dcooperdalrymple/pico_synth_sandbox-hardware/3dmodels/raspberry-pi-pico/RT6150B-33GQW.step

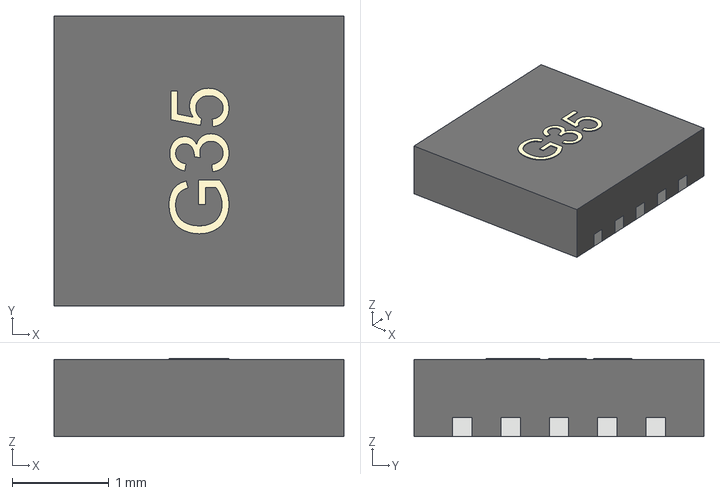
[picture p20: CAD file, 2023-11-14]
3dmodels/raspberry-pi-pico/RT6150B-33GQW.step
3.00 x 3.00 x 0.81 mm
