dcooperdalrymple/pico_synth_sandbox-hardware/3dmodels/SJ1-3525N/ST-212.step

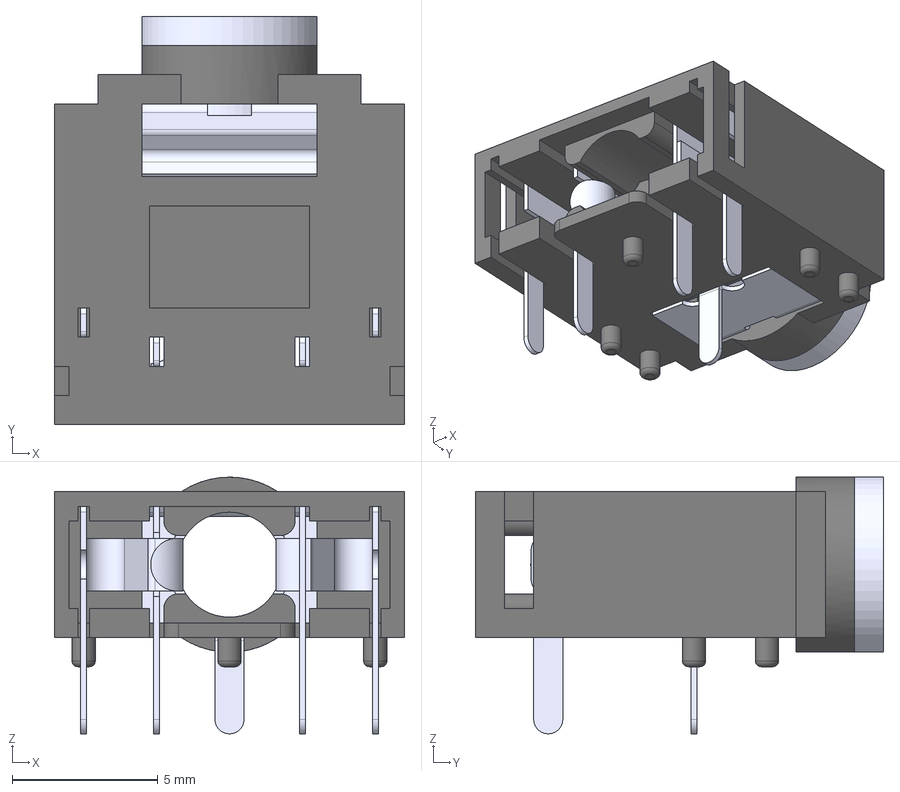
[picture p21: CAD file, 2023-11-14]
3dmodels/SJ1-3525N/ST-212.step
12.0 x 14.0 x 8.80 mm
