dcooperdalrymple/pico_synth_sandbox-hardware/case/rev2/pico_synth_sandbox-Rev2-Bottom.stl

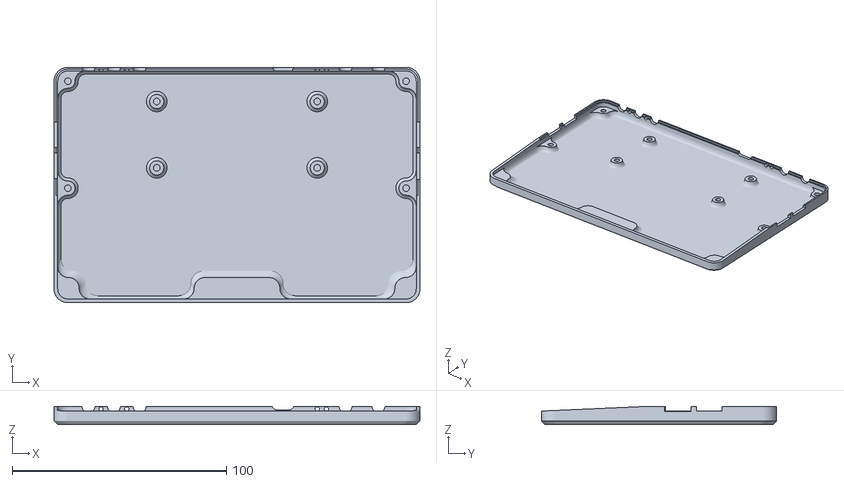
[picture p22: CAD file, 2024-02-06]
case/rev2/pico_synth_sandbox-Rev2-Bottom.stl
171.0 x 110.0 x 8.55
