dcooperdalrymple/pico_synth_sandbox-hardware/3dmodels/PJ320D/PJ320D-Pin-B.SLDPRT

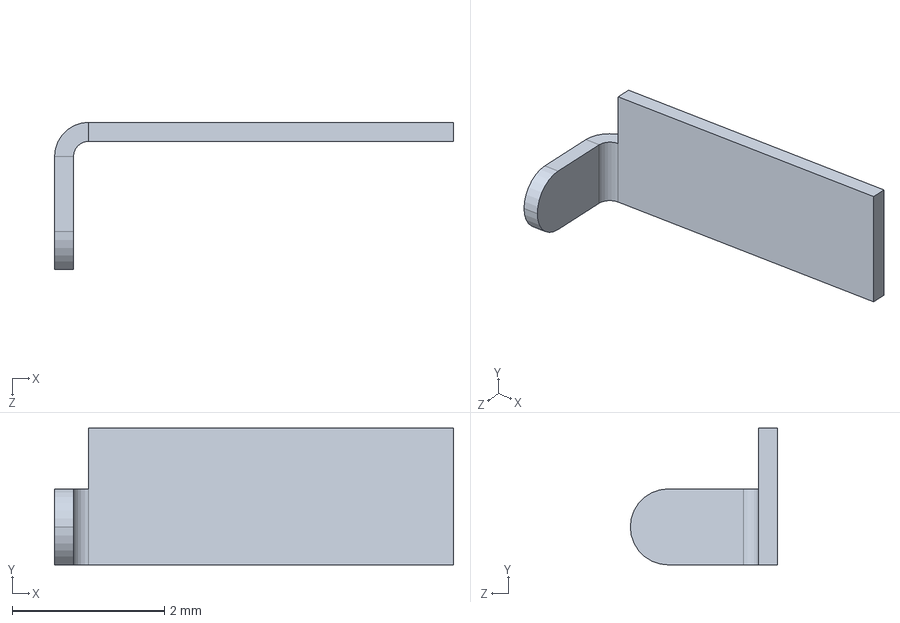
[picture p23: CAD file, 2024-01-01]
3dmodels/PJ320D/PJ320D-Pin-B.SLDPRT
5.25 x 1.80 x 1.94 mm
