dcooperdalrymple/pico_synth_sandbox-hardware/3dmodels/raspberry-pi-pico/C0603.step

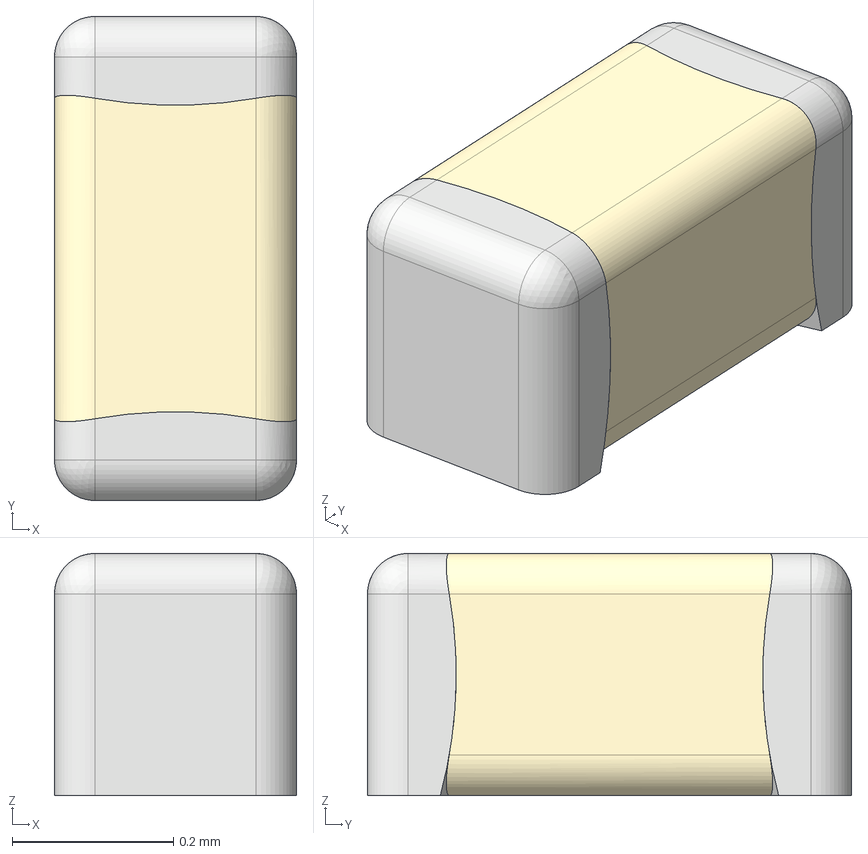
[picture p24: CAD file, 2023-11-14]
3dmodels/raspberry-pi-pico/C0603.step
0.3 x 0.6 x 0.3 mm
