dcooperdalrymple/pico_synth_sandbox-hardware/case/rev2/pico_synth_sandbox-Rev2-Switch.stl

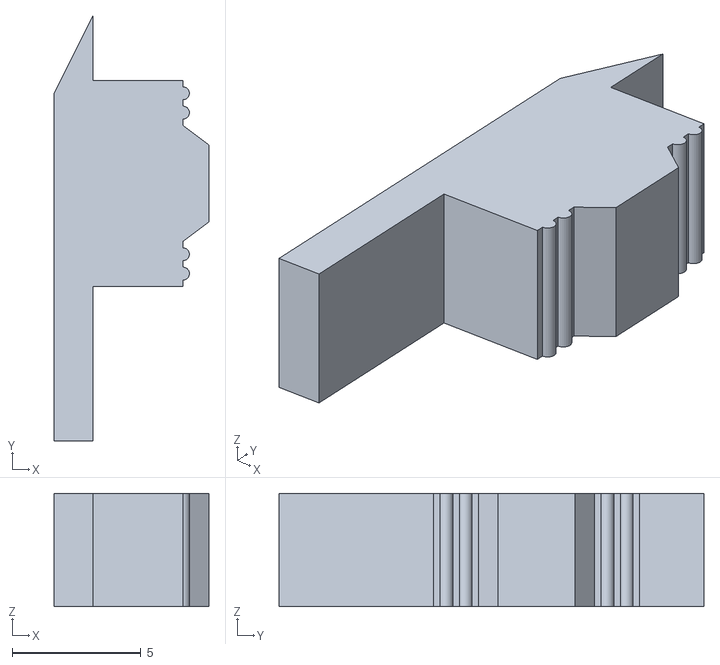
[picture p25: CAD file, 2024-02-06]
case/rev2/pico_synth_sandbox-Rev2-Switch.stl
6.00 x 16.5 x 4.40
