dcooperdalrymple/pico_synth_sandbox-hardware/3dmodels/PJ320D/PJ320A.SLDPRT

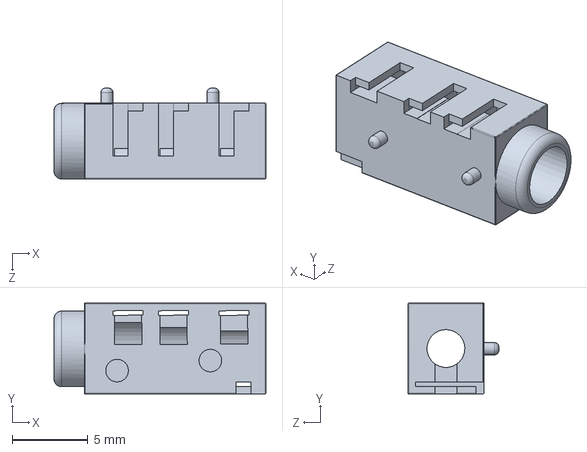
[picture p26: CAD file, 2024-01-01]
3dmodels/PJ320D/PJ320A.SLDPRT
14.0 x 6.00 x 6.00 mm
