dcooperdalrymple/pico_synth_sandbox-hardware/3dmodels/raspberry-pi-pico/R0603.step

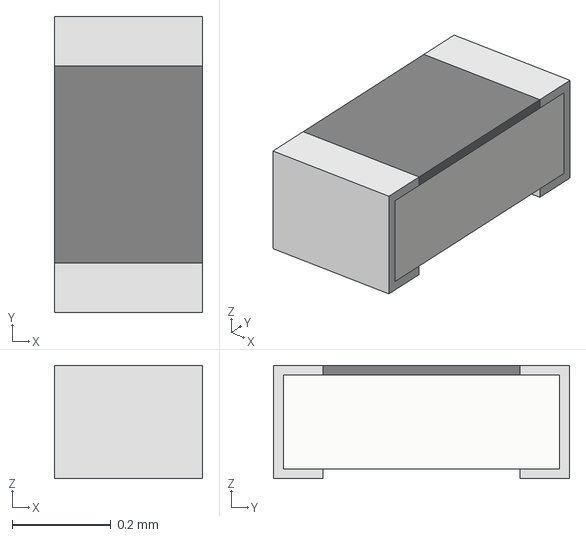
[picture p27: CAD file, 2023-11-14]
3dmodels/raspberry-pi-pico/R0603.step
0.3 x 0.6 x 0.23 mm
