dcooperdalrymple/pico_synth_sandbox-hardware/case/rev2/pico_synth_sandbox-Rev2-LcdHeader.stl

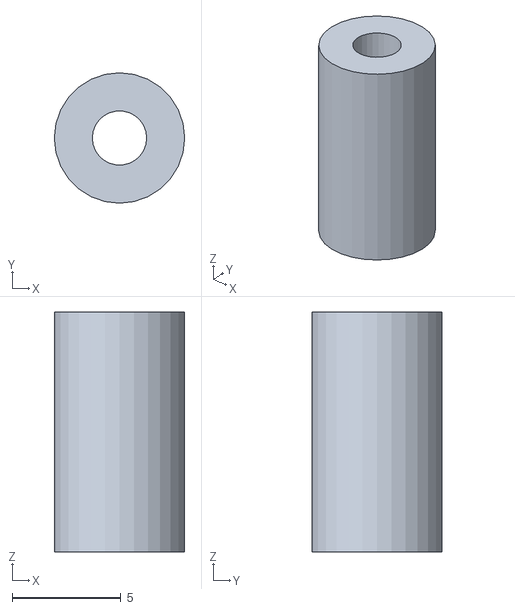
[picture p28: CAD file, 2024-02-06]
case/rev2/pico_synth_sandbox-Rev2-LcdHeader.stl
6.00 x 6.00 x 11.0
