dcooperdalrymple/pico_synth_sandbox-hardware/3dmodels/raspberry-pi-pico/TactSwitch.step

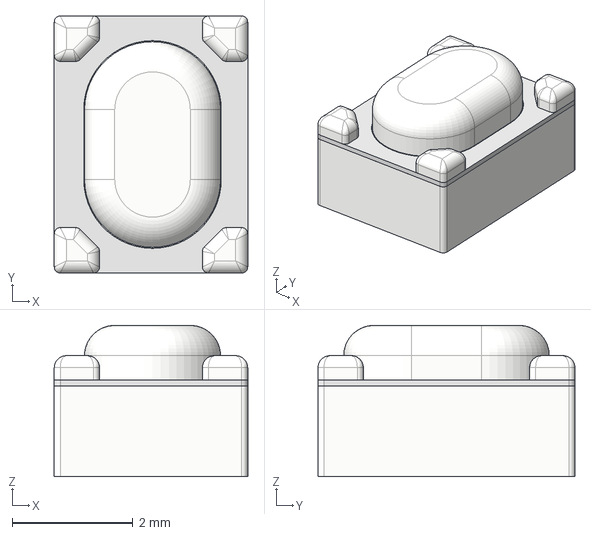
[picture p29: CAD file, 2023-11-14]
3dmodels/raspberry-pi-pico/TactSwitch.step
3.20 x 4.25 x 2.50 mm
