dcooperdalrymple/pico_synth_sandbox-hardware/3dmodels/raspberry-pi-pico/R1005.step

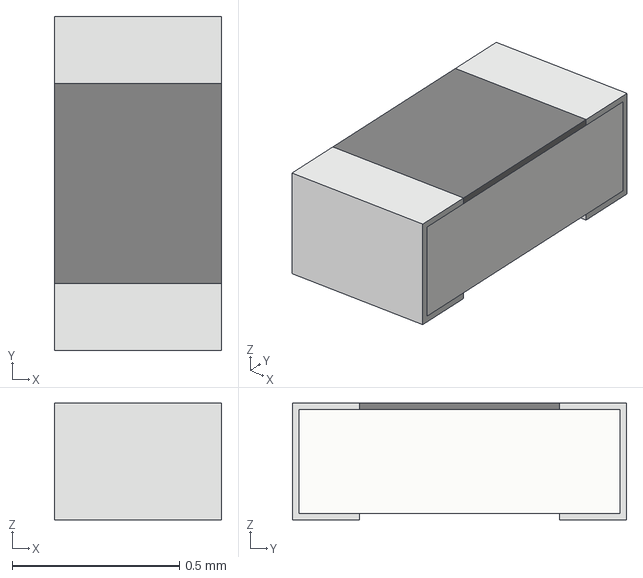
[picture p30: CAD file, 2023-11-14]
3dmodels/raspberry-pi-pico/R1005.step
0.5 x 1.00 x 0.35 mm
