dcooperdalrymple/pico_synth_sandbox-hardware/3dmodels/raspberry-pi-pico/W25Q16JV_UX.step

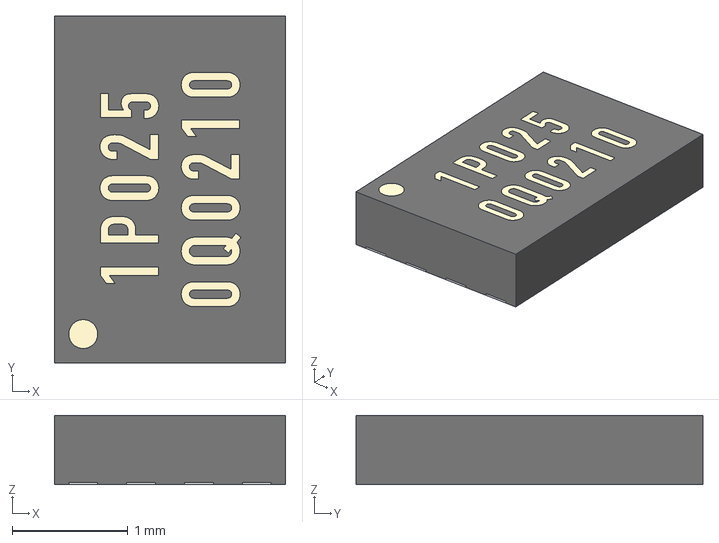
[picture p31: CAD file, 2023-11-14]
3dmodels/raspberry-pi-pico/W25Q16JV_UX.step
2.00 x 3.00 x 0.6 mm
