dcooperdalrymple/pico_synth_sandbox-hardware/3dmodels/raspberry-pi-pico/Inductor.step

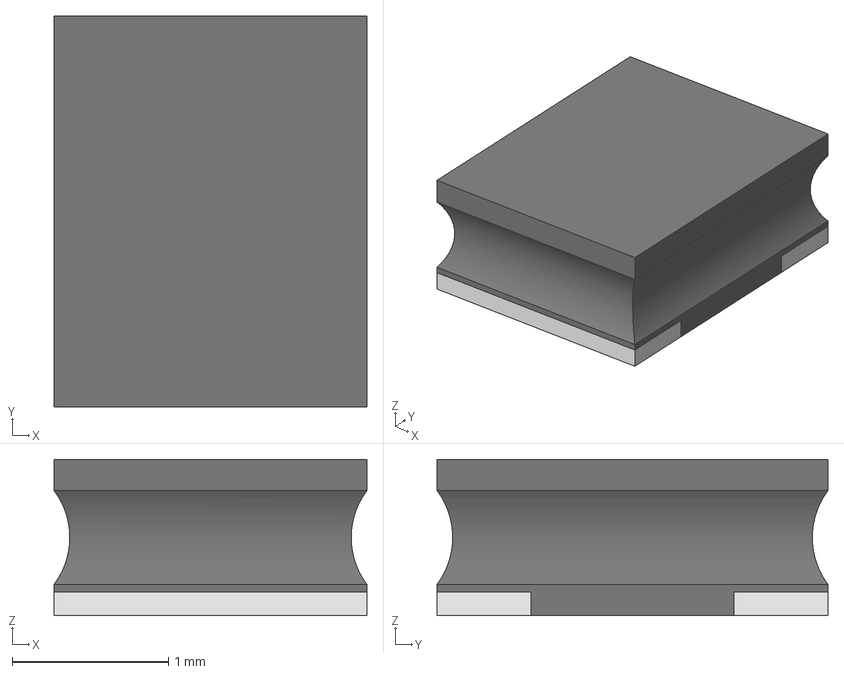
[picture p32: CAD file, 2023-11-14]
3dmodels/raspberry-pi-pico/Inductor.step
2.00 x 2.50 x 1.00 mm
