dcooperdalrymple/pico_synth_sandbox-hardware/3dmodels/raspberry-pi-pico/R1608.step

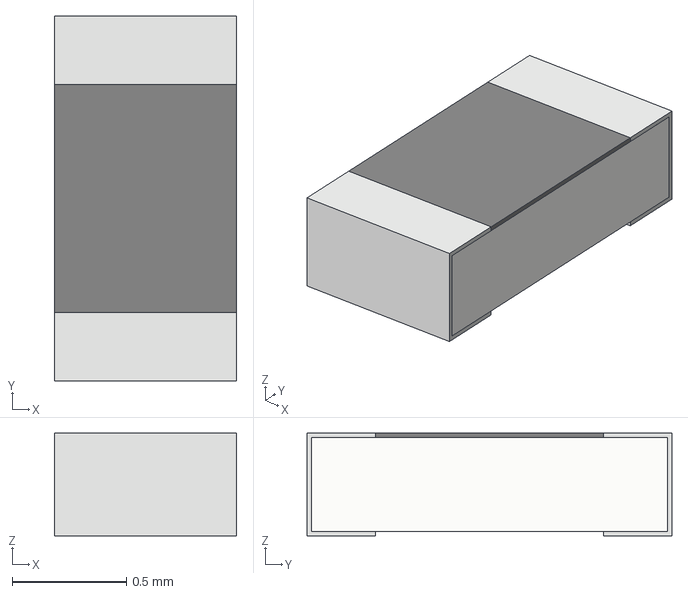
[picture p33: CAD file, 2023-11-14]
3dmodels/raspberry-pi-pico/R1608.step
0.8 x 1.60 x 0.45 mm
