dcooperdalrymple/pico_synth_sandbox-hardware/3dmodels/raspberry-pi-pico/USB microB.step

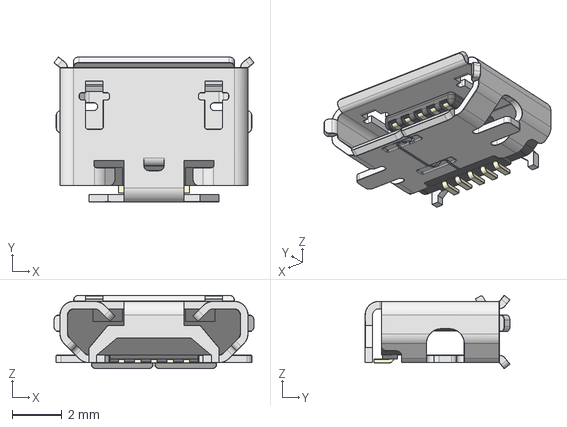
[picture p34: CAD file, 2023-11-14]
3dmodels/raspberry-pi-pico/USB microB.step
8.01 x 5.80 x 2.94 mm
