dcooperdalrymple/pico_synth_sandbox-hardware/3dmodels/raspberry-pi-pico/LED1608_t4.step

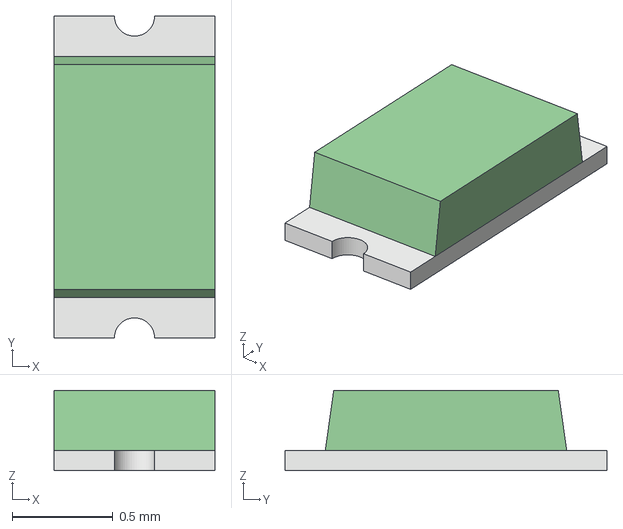
[picture p35: CAD file, 2023-11-14]
3dmodels/raspberry-pi-pico/LED1608_t4.step
0.8 x 1.60 x 0.4 mm
