dcooperdalrymple/pico_synth_sandbox-hardware/3dmodels/raspberry-pi-pico/C2012.step

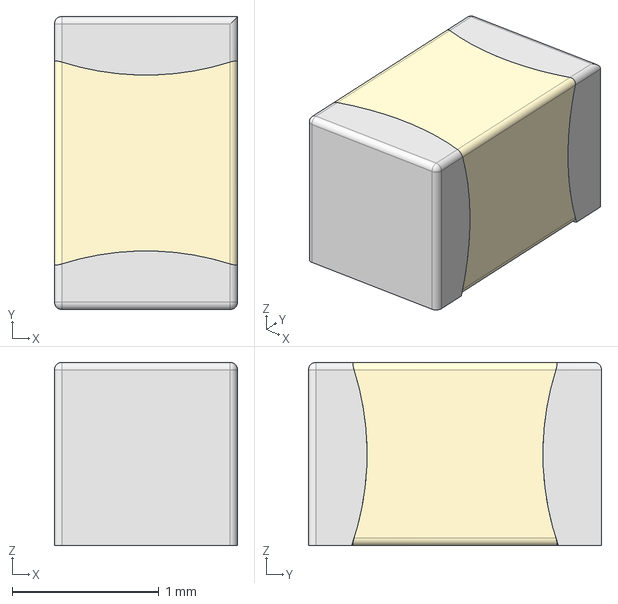
[picture p36: CAD file, 2023-11-14]
3dmodels/raspberry-pi-pico/C2012.step
1.25 x 2.00 x 1.25 mm
