dcooperdalrymple/pico_synth_sandbox-hardware/3dmodels/raspberry-pi-pico/Transistor.step

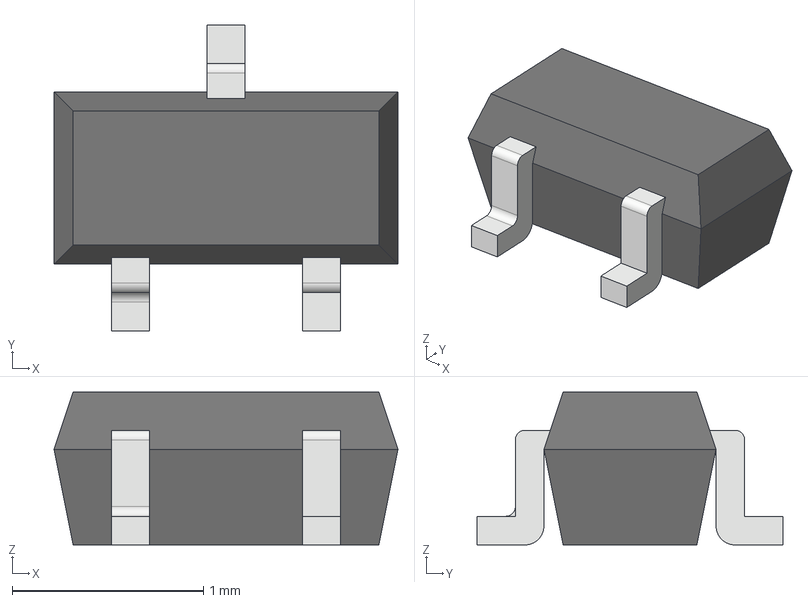
[picture p37: CAD file, 2023-11-14]
3dmodels/raspberry-pi-pico/Transistor.step
1.80 x 1.60 x 0.8 mm
