dcooperdalrymple/pico_synth_sandbox-hardware/3dmodels/raspberry-pi-pico/CrystalUnit.step

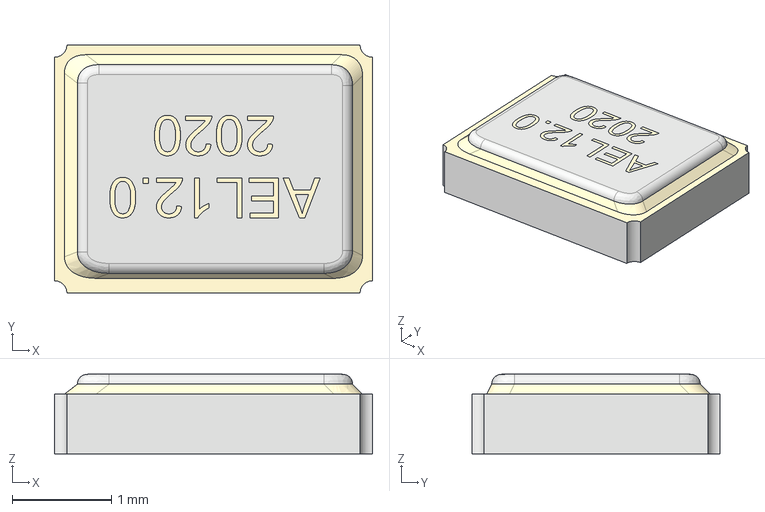
[picture p38: CAD file, 2023-11-14]
3dmodels/raspberry-pi-pico/CrystalUnit.step
3.20 x 2.50 x 0.8 mm
