dcooperdalrymple/pico_synth_sandbox-hardware/3dmodels/raspberry-pi-pico/CircuitBoard_Raspberry Pi Pico.step

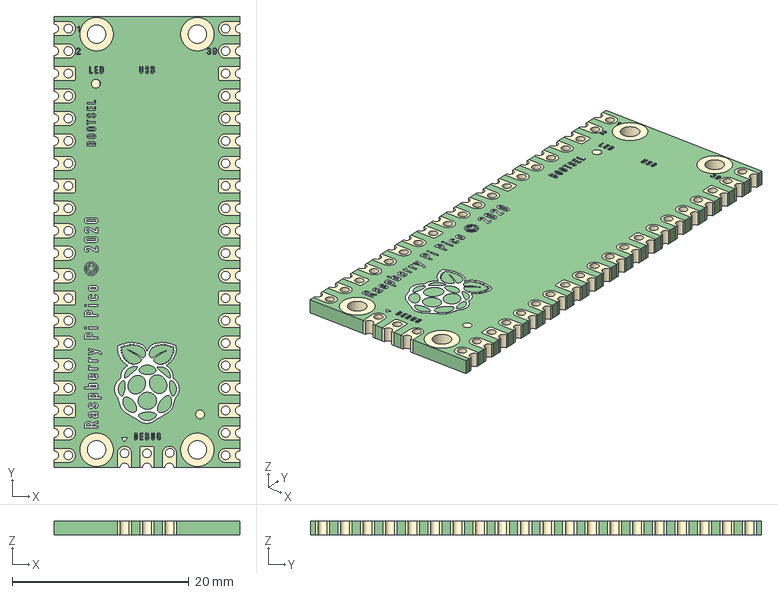
[picture p40: CAD file, 2023-11-14]
3dmodels/raspberry-pi-pico/CircuitBoard_Raspberry Pi Pico.step
21.0 x 51.0 x 1.61 mm
